Mithilessh2010/Split-Keyboard-Hackclub/Images/Screen Shot 2025-12-02 at 9.31.10 PM.png

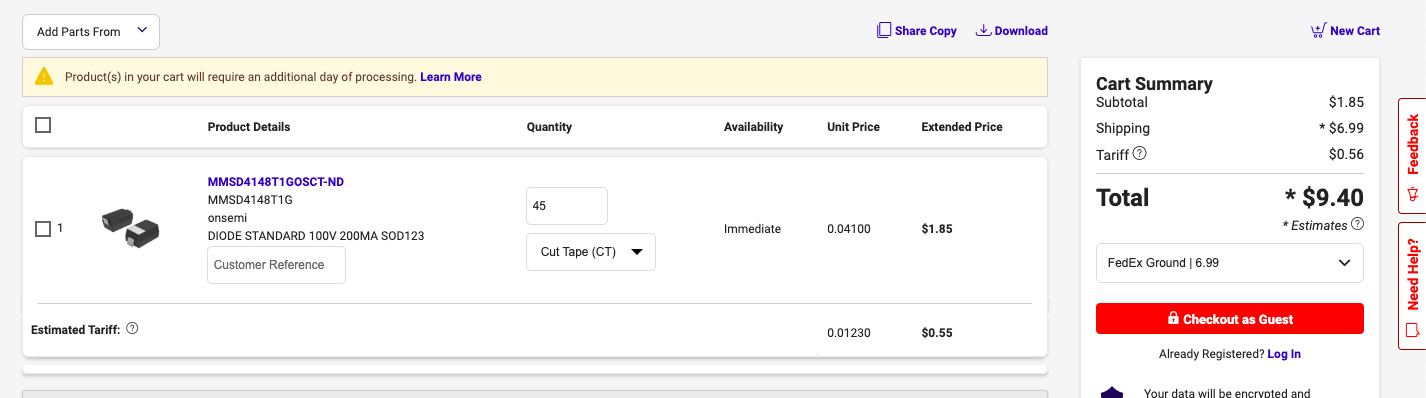
Images/Screen Shot 2025-12-02 at 9.31.10 PM.png
