Mithilessh2010/Split-Keyboard-Hackclub/Images/Screen Shot 2025-12-02 at 9.31.47 PM.png

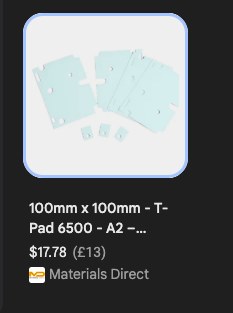
Images/Screen Shot 2025-12-02 at 9.31.47 PM.png
